nliaudat/weatherstation/imgs/2021-06-02 18.09.57.jpg

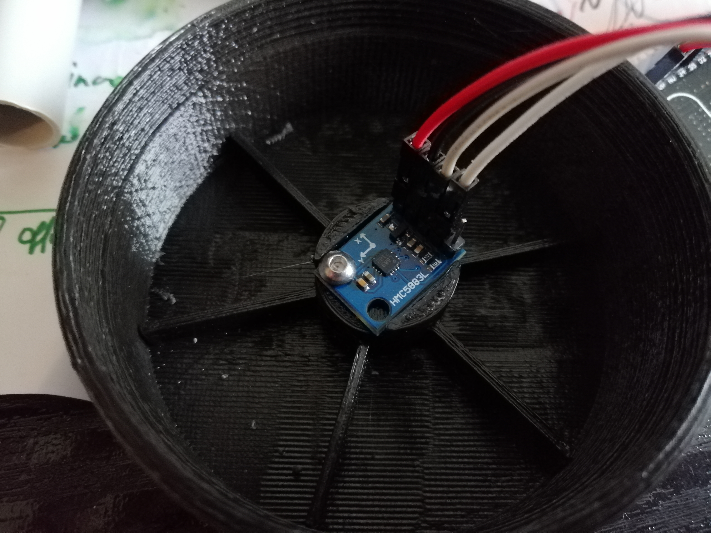
imgs/2021-06-02 18.09.57.jpg
