nliaudat/weatherstation/imgs/2021-06-18 13.28.30.jpg

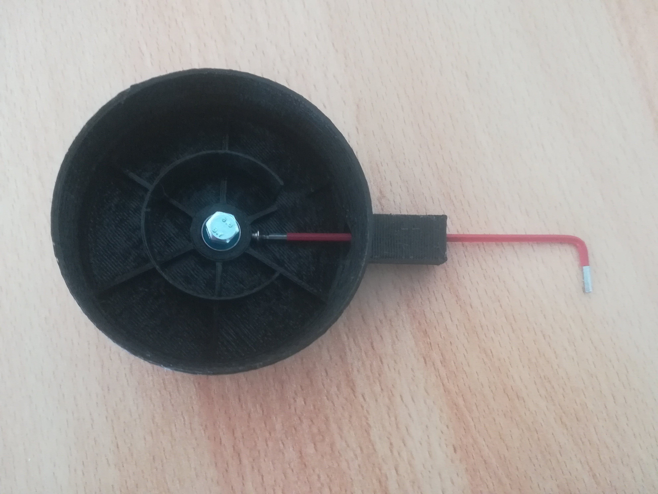
imgs/2021-06-18 13.28.30.jpg
