nliaudat/weatherstation/imgs/cables_managemnt.jpg

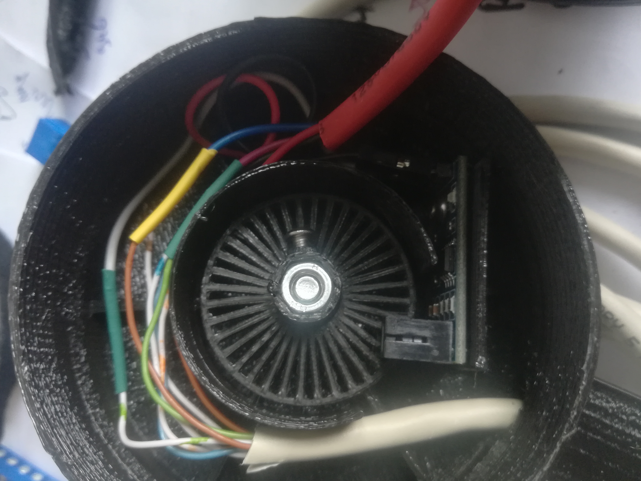
imgs/cables_managemnt.jpg
