nliaudat/weatherstation/imgs/drill_5mm_for_rj45.jpg

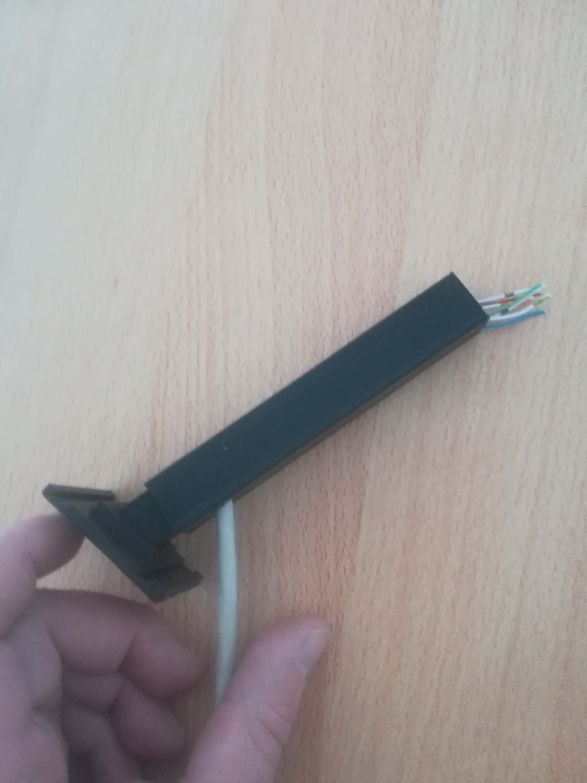
imgs/drill_5mm_for_rj45.jpg
