nliaudat/weatherstation/imgs/axles_mounting_instruction.png

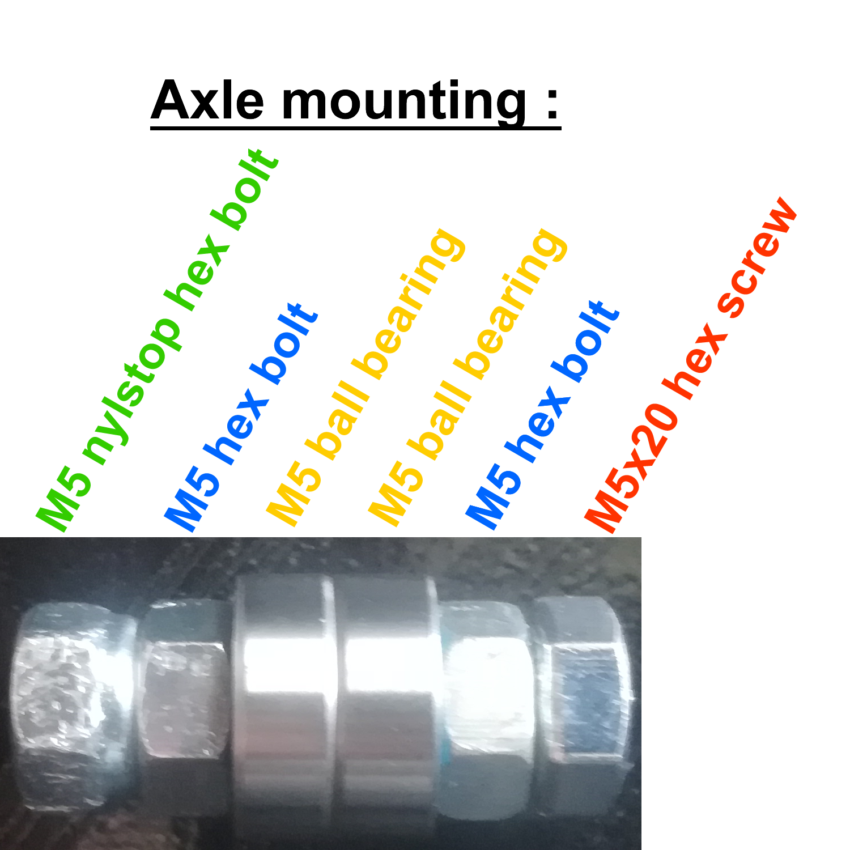
imgs/axles_mounting_instruction.png
