nliaudat/weatherstation/imgs/wiring.png

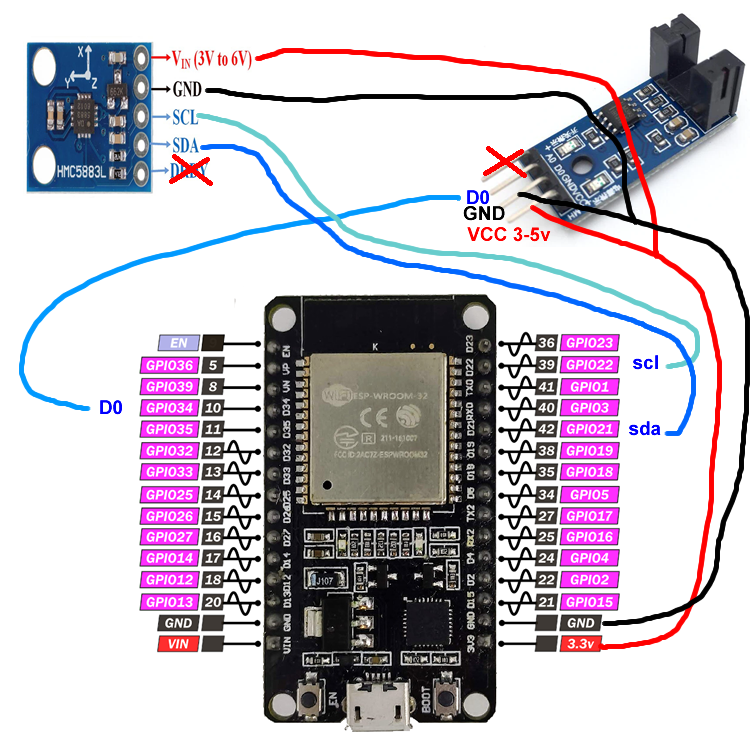
imgs/wiring.png
